rohankalbag/iot-biogas-health-monitoring/Source Code/firmware/drivers/i2c_conn.h

// Electronic Design Lab EE 344 IIT Bombay
// Team Tue: 23 
// Authors: Sankalp Bhamare, Rohan Rajesh Kalbag, Jujhaar Singh

#ifndef I2C_CONN_H
#define I2C_CONN_H

#include "i2c_global.h"
#include "acd10_driver.h"
#include "dht20_driver.h"
#include "lcd_driver.h"
#include "buzzer_driver.h"

void init_i2c();
void denit_i2c();
#endif
