rohankalbag/iot-biogas-health-monitoring/Source Code/firmware/drivers/i2c_global.h

// Electronic Design Lab EE 344 IIT Bombay
// Team Tue: 23 
// Authors: Sankalp Bhamare, Rohan Rajesh Kalbag, Jujhaar Singh

// header file containing the I2C communication protocol parameters

#define I2C_MASTER_SCL_IO 22        /*!< GPIO number used for I2C master clock */
#define I2C_MASTER_SDA_IO 21        /*!< GPIO number used for I2C master data  */
#define I2C_MASTER_NUM 0            /*!< I2C master i2c port number, the number of i2c peripheral interfaces available will depend on the chip */
#define I2C_MASTER_FREQ_HZ 10000    /*!< I2C master clock frequency */
#define I2C_MASTER_TX_BUF_DISABLE 0 /*!< I2C master doesn't need buffer */
#define I2C_MASTER_RX_BUF_DISABLE 0 /*!< I2C master doesn't need buffer */
#define I2C_MASTER_TIMEOUT_MS 1000

#include <stdio.h>
#include "esp_log.h"
#include "driver/i2c.h"

char Calc_CRC8(char *data, unsigned char Num);
