rohankalbag/iot-biogas-health-monitoring/Source Code/firmware/server_conn.h

// Electronic Design Lab EE 344 IIT Bombay
// Team Tue: 23 
// Authors: Sankalp Bhamare, Rohan Rajesh Kalbag, Jujhaar Singh

#ifndef SERVER_CONN_H
#define SERVER_CONN_H

#include <string.h>
#include "freertos/FreeRTOS.h"
#include "freertos/task.h"
#include "freertos/event_groups.h"
#include "esp_system.h"
#include "esp_wifi.h"
#include "esp_event.h"
#include "esp_log.h"
#include "nvs_flash.h"

#include "lwip/err.h"
#include "lwip/sys.h"

#include <sys/param.h>
#include <stdlib.h>
#include <ctype.h>
#include "esp_log.h"
#include "nvs_flash.h"
#include "esp_event.h"
#include "esp_netif.h"

#include "freertos/FreeRTOS.h"
#include "freertos/task.h"
#include "esp_system.h"

#include "esp_http_client.h"

#define WEB_SERVER "192.168.160.135"
#define WEB_PORT "5000"
#define WEB_PATH "/"

#include "lwip/err.h"
#include "lwip/sockets.h"
#include "lwip/sys.h"
#include "lwip/netdb.h"
#include "lwip/dns.h"
#include "sdkconfig.h"

#define MAX_HTTP_RECV_BUFFER 512
#define MAX_HTTP_OUTPUT_BUFFER 2048
#define MAX_HTTP_RETRIES 100

// WiFi hotspot or access point credentials
#define ESP_WIFI_SSID "RnD"
#define ESP_WIFI_PASS "12345678"
#define ESP_MAXIMUM_RETRY 100 // maximum number of tries
#define ESP_WIFI_SCAN_AUTH_MODE_THRESHOLD WIFI_AUTH_OPEN

#define WIFI_CONNECTED_BIT BIT0
#define WIFI_FAIL_BIT BIT1

esp_err_t wifi_init_sta(void);
esp_err_t http_post_task(int co2_ppm, float humidity);
#endif
